mdaeron/pypl/pictures/adafruit_3263.png

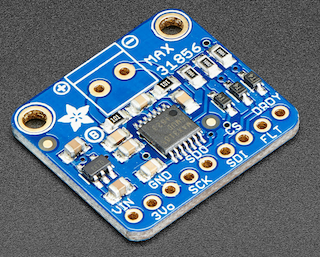
pictures/adafruit_3263.png
