mdaeron/pypl/pictures/heating_element.png

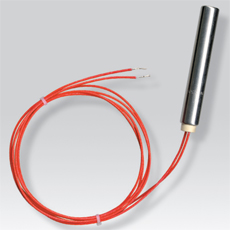
pictures/heating_element.png
