mdaeron/pypl/pictures/mcp23017.png

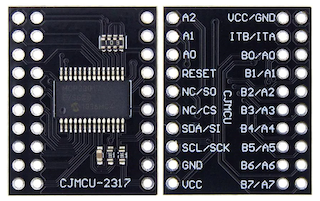
pictures/mcp23017.png
