mdaeron/pypl/pictures/motherboard.png

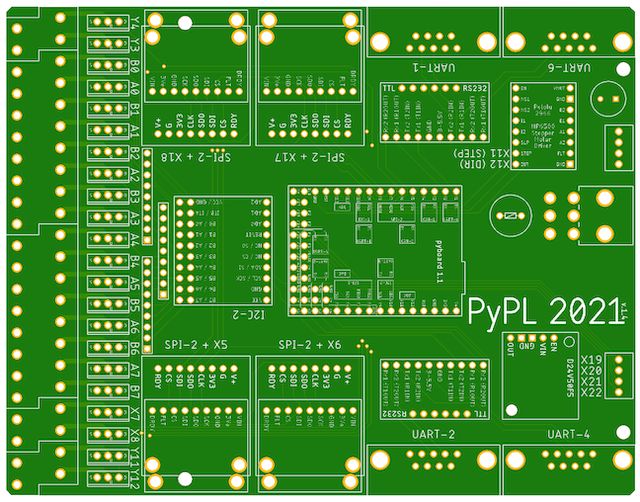
pictures/motherboard.png
