mdaeron/pypl/pictures/pyboard.png

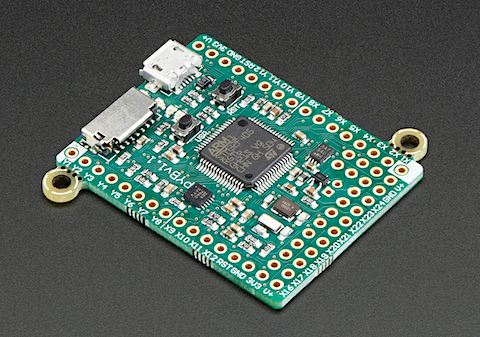
pictures/pyboard.png
